liam-tirpitz/RoomMate/client/room-occupancy/Room-Occupancy-Client/include/SysConfig.h

#ifndef SYSCONF_H
#define SYSCONF_H

#include <Arduino.h>
#include <Storage.h>
#include <WiFi.h>

#define VBATPIN A13
#define uS_TO_S_FACTOR 1000000ull  /* Conversion factor for micro seconds to seconds */
#define WIFI_CONNECT_TIMEOUT_MS 20000

class SysConfig {
    public:
        SysConfig();
        void sleep();
        void configDefaultSleep();
        int readBatteryVoltage();
        void setup_wifi_connection();
    private:
        Storage storage;
};

#endif
